qiao-bridge/jms583-hard-drive-box/assets/渲染图.PNG

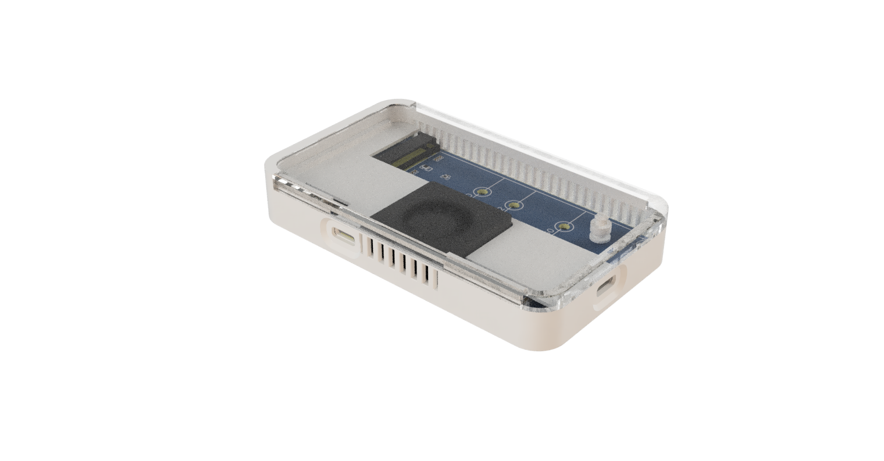
assets/渲染图.PNG
