qiao-bridge/jms583-hard-drive-box/docs/阻抗匹配.png

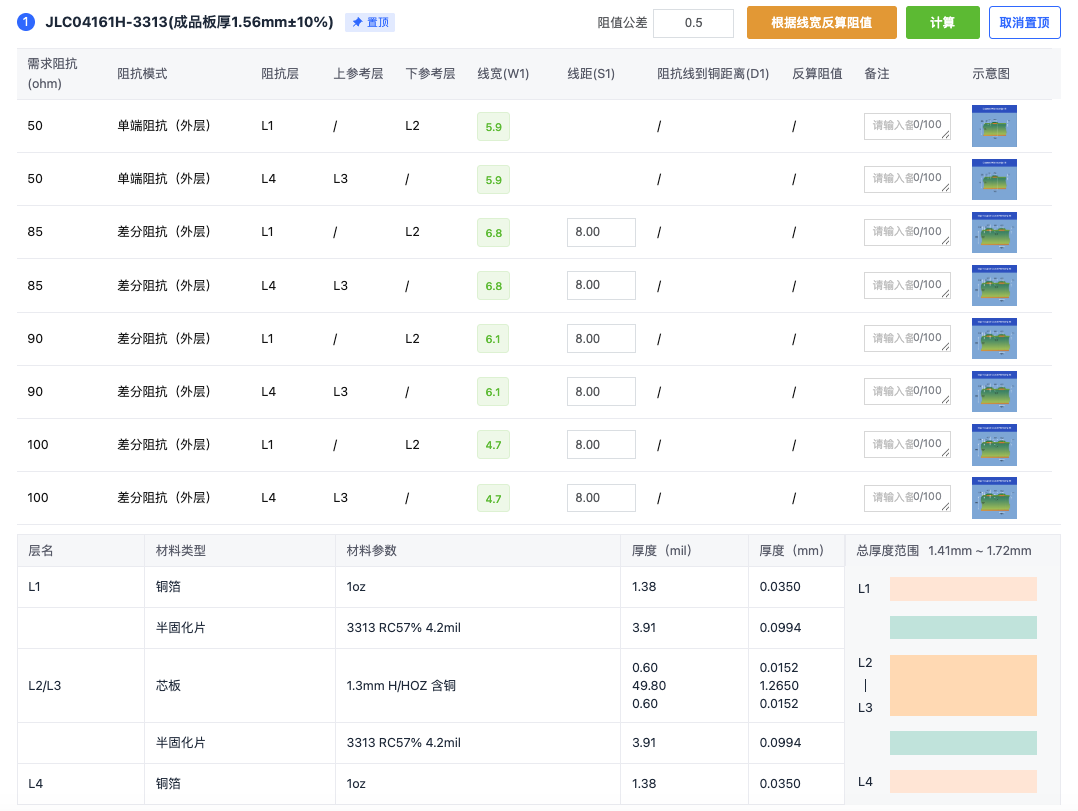
docs/阻抗匹配.png
